TMRCI-DEV1/Nano-SMINI/KiCad/3D_Models/185163-3.jpg

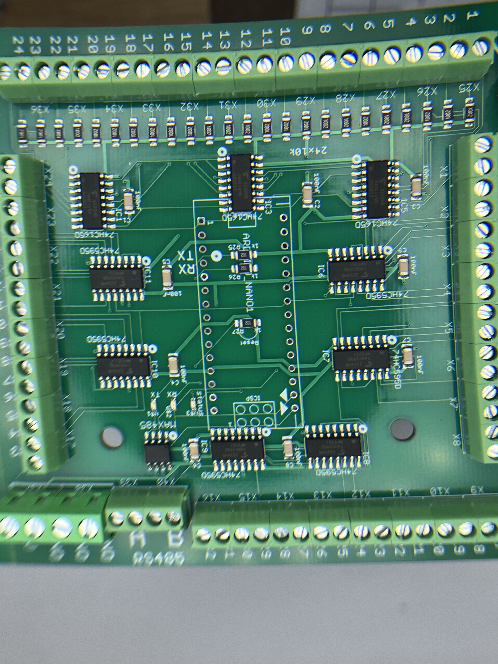
KiCad/3D_Models/185163-3.jpg
